murrayinglis/EEE3088-group-09/Simulation/UVLO.asc

D1: zener
M2: pmos
R1: res; 3.6Meg
R2: res; 3Meg
R3: res; 2.05Meg
R4: res; 150k
R5: res; 1Meg
R6: res; 10Meg
R7: res; 100k
U1: OP07
V1: voltage; ""; Rser=0.01
Named nets: 0
.dc V1 5 0
